reverse2013/ReVerSE-U8/u8_tsconf/rtl/rtc/CMOS_TRDOS/TR-DOS.JPG

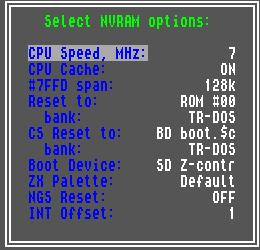
u8_tsconf/rtl/rtc/CMOS_TRDOS/TR-DOS.JPG
