reverse2013/ReVerSE-U8/u8_tsconf/rtl/rtc/CMOS_VTRDOS/WC vs VTRDOS.JPG

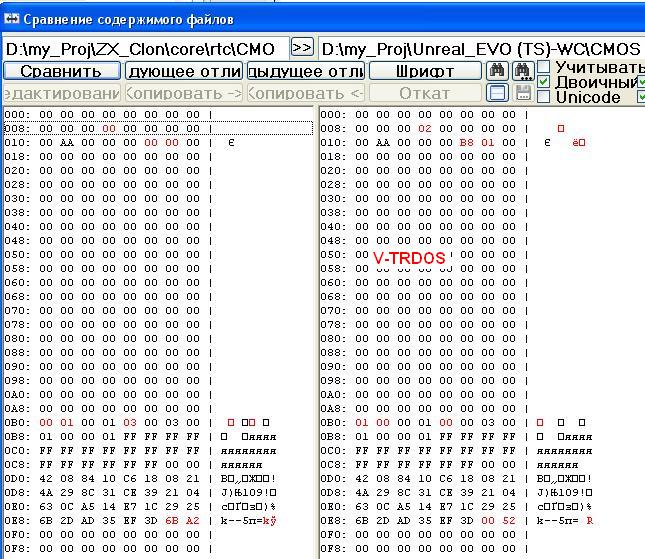
u8_tsconf/rtl/rtc/CMOS_VTRDOS/WC vs VTRDOS.JPG
