reverse2013/ReVerSE-U8/u8_tsconf/rtl/rtc/CMOS_WC/WC.JPG

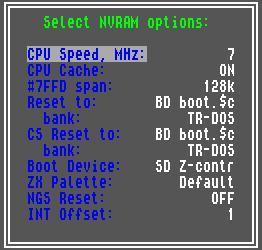
u8_tsconf/rtl/rtc/CMOS_WC/WC.JPG
