reverse2013/ReVerSE-U8/u8_vector/doc/jtag_statemachine.png

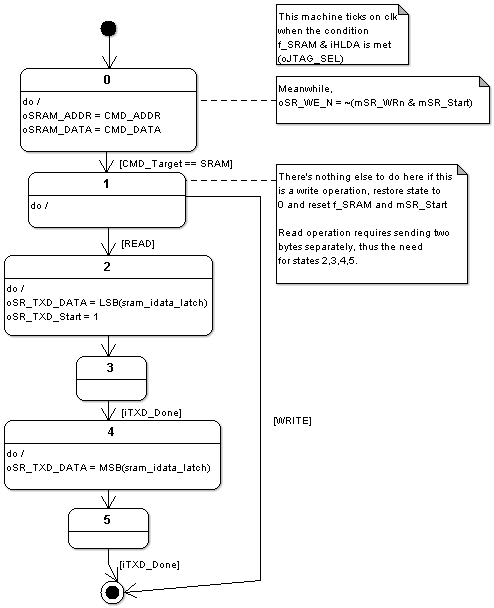
u8_vector/doc/jtag_statemachine.png
