reverse2013/ReVerSE-U8/u8_vector/doc/putupchik.jpg

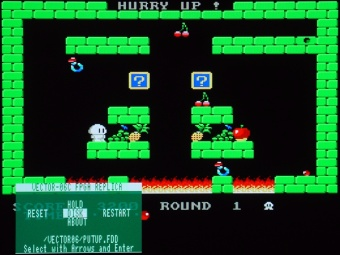
u8_vector/doc/putupchik.jpg
